bonnette/Pac_Clock/photos/pac_setup.jpg

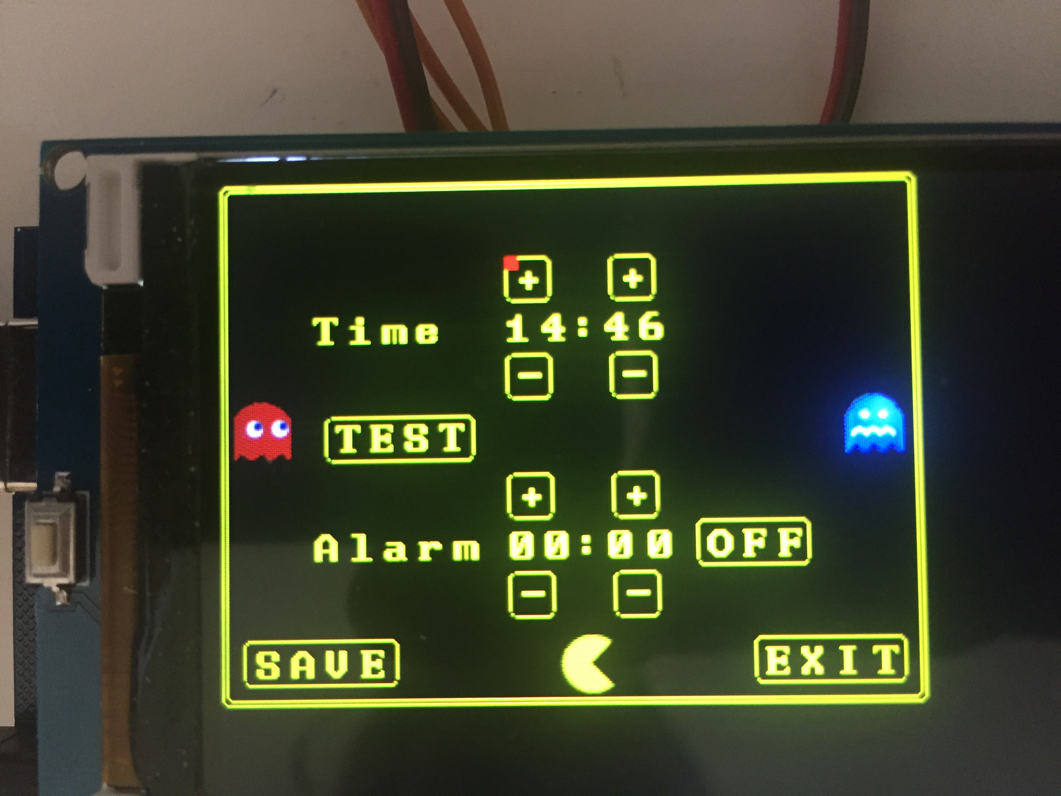
photos/pac_setup.jpg
